dinoflorenzi/THOMSON-MO-TO-SOUNDCARD/SN76489AN/IMG_20201018_101340.jpg

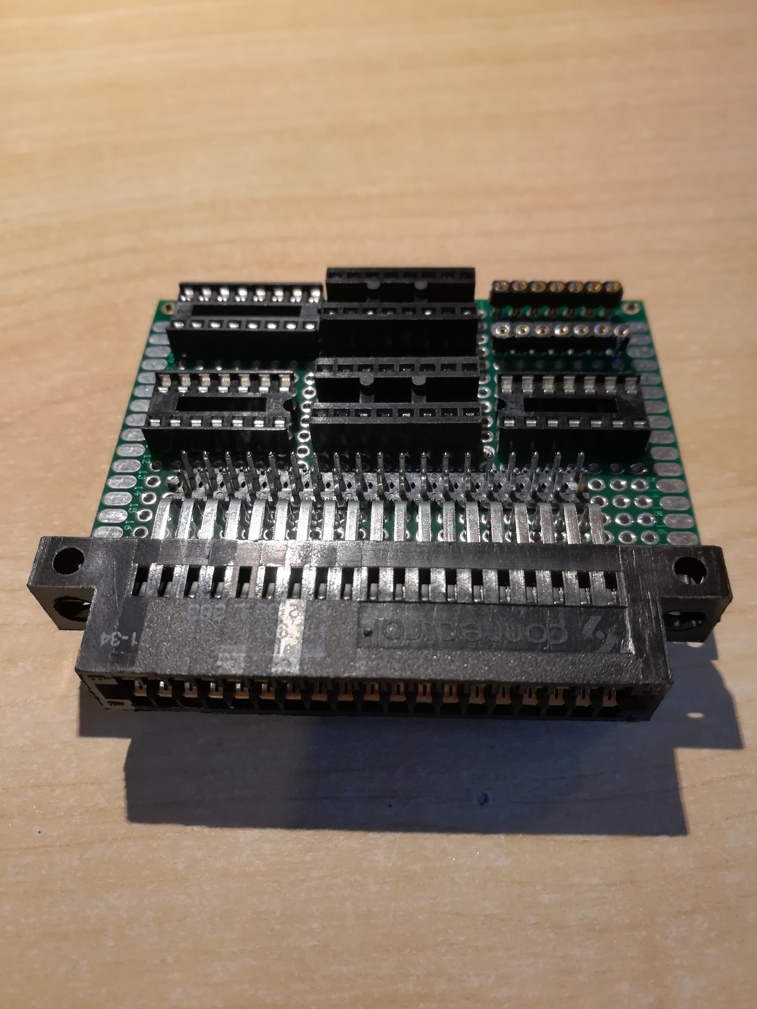
SN76489AN/IMG_20201018_101340.jpg
