dinoflorenzi/THOMSON-MO-TO-SOUNDCARD/SN76489AN/IMG_20201108_161605.jpg

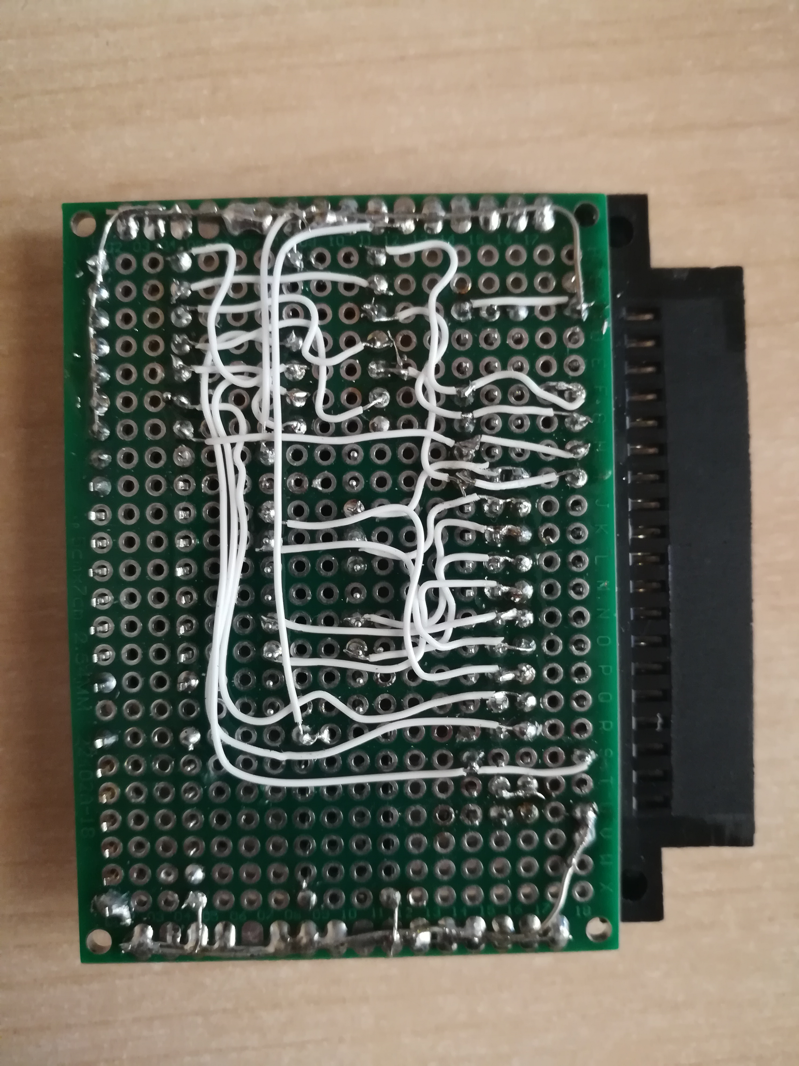
SN76489AN/IMG_20201108_161605.jpg
