dinoflorenzi/THOMSON-MO-TO-SOUNDCARD/SN76489AN/IMG_20201115_202511.jpg

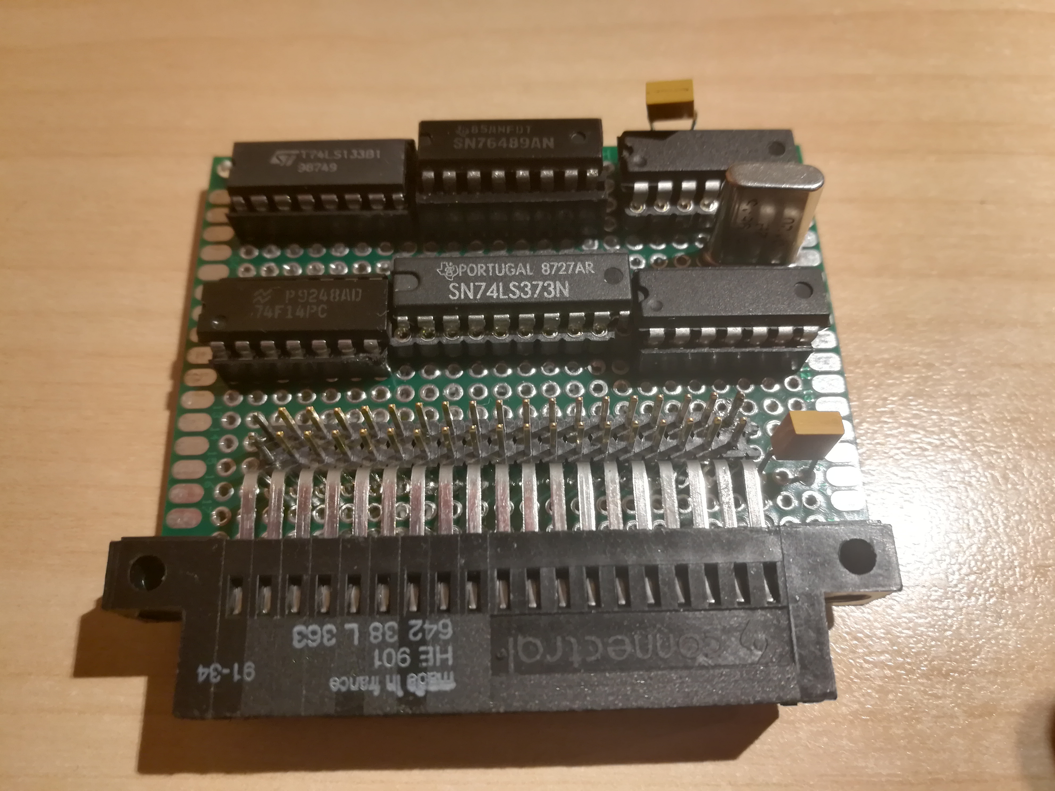
SN76489AN/IMG_20201115_202511.jpg
