dinoflorenzi/THOMSON-MO-TO-SOUNDCARD/SN76489AN/IMG_20210108_192748.jpg

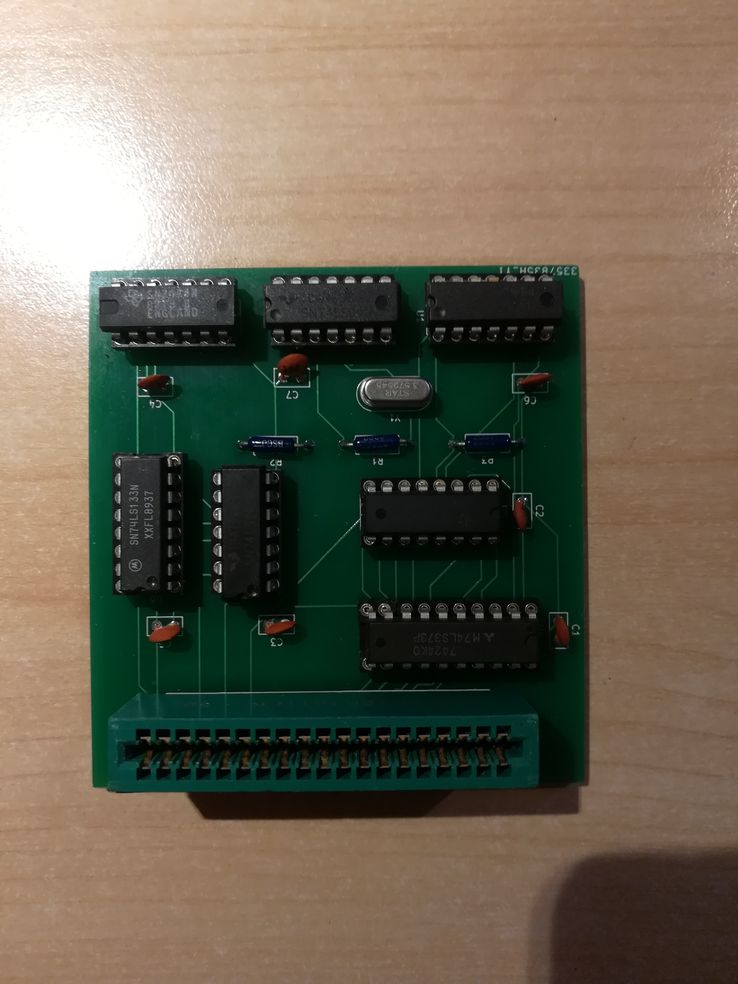
SN76489AN/IMG_20210108_192748.jpg
