dinoflorenzi/THOMSON-MO-TO-SOUNDCARD/SN76489AN/SN76489_MOTO.png

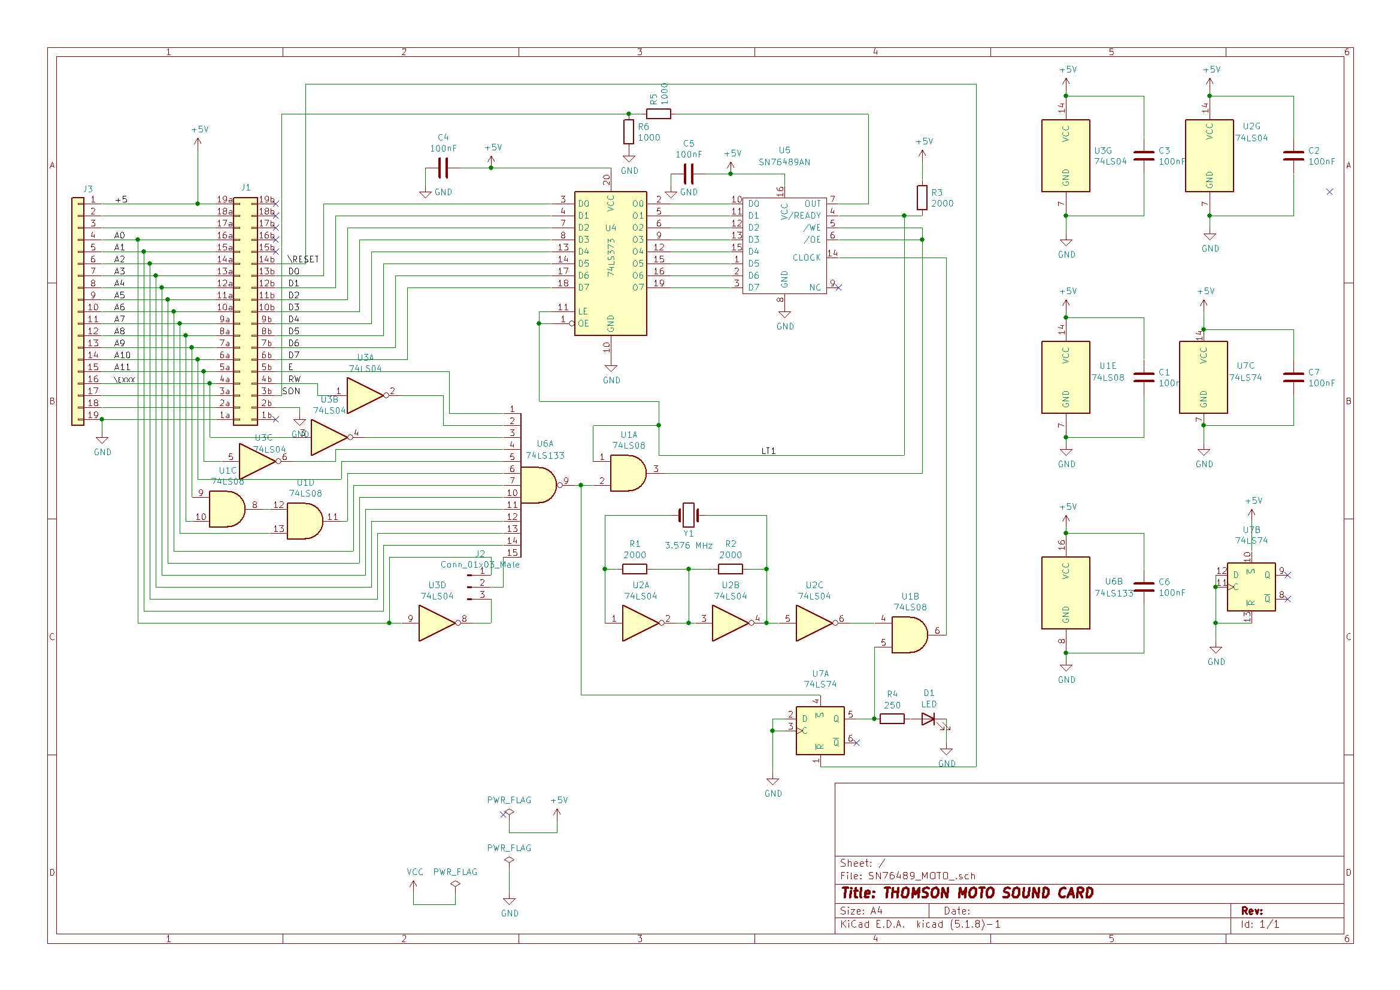
SN76489AN/SN76489_MOTO.png
