dinoflorenzi/THOMSON-MO-TO-SOUNDCARD/SN76489AN/sn76489_REV2.jpg

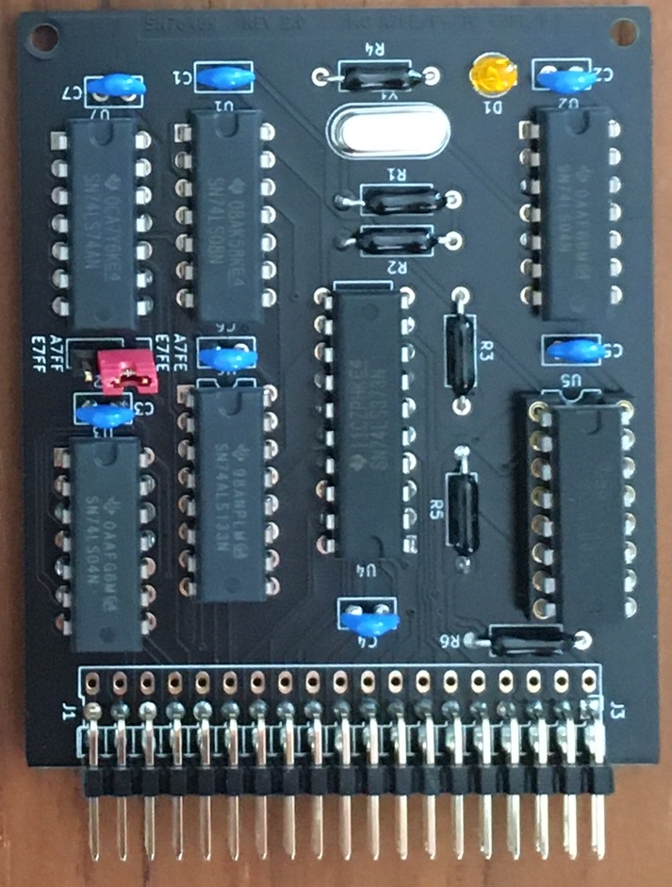
SN76489AN/sn76489_REV2.jpg
