dinoflorenzi/THOMSON-MO-TO-SOUNDCARD/YM2413/IMG_20210620_180053.jpg

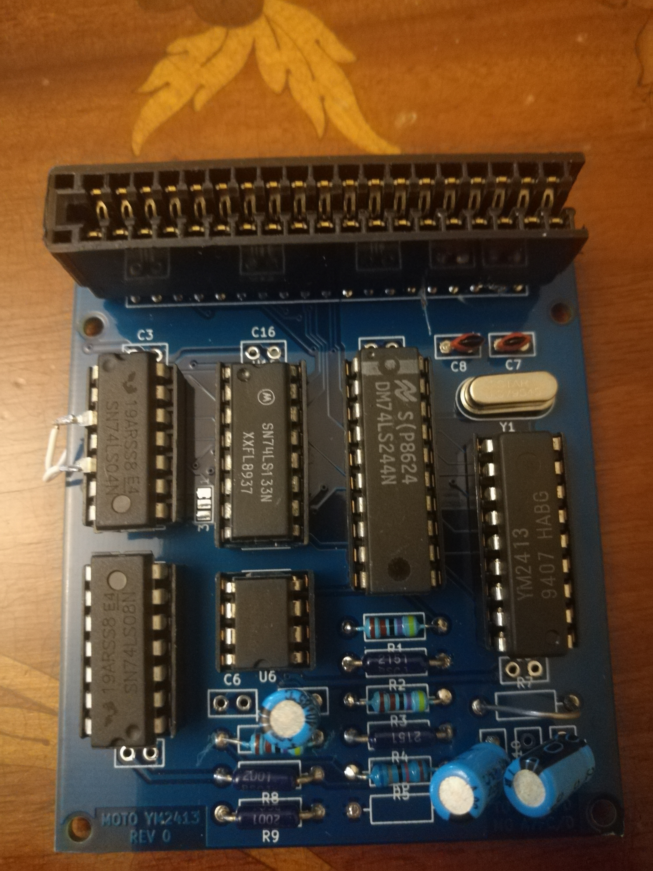
YM2413/IMG_20210620_180053.jpg
