dinoflorenzi/THOMSON-MO-TO-SOUNDCARD/YM2413/REV2/YM2413_FOOL_054410.png

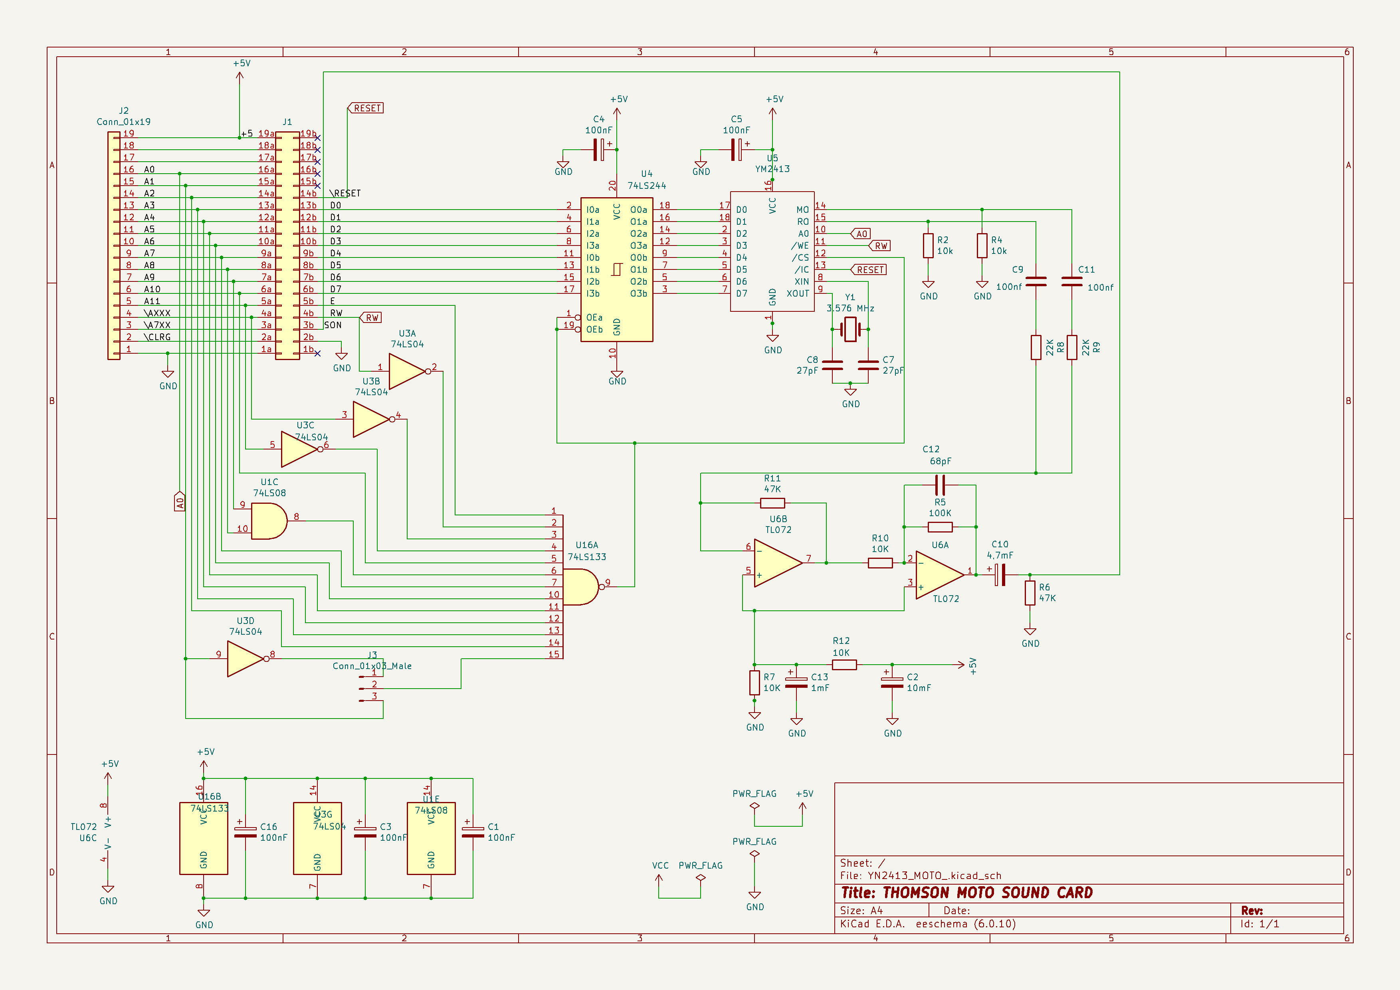
YM2413/REV2/YM2413_FOOL_054410.png
