dinoflorenzi/THOMSON-MO-TO-SOUNDCARD/YM2413/YM2413_MOTO.jpg

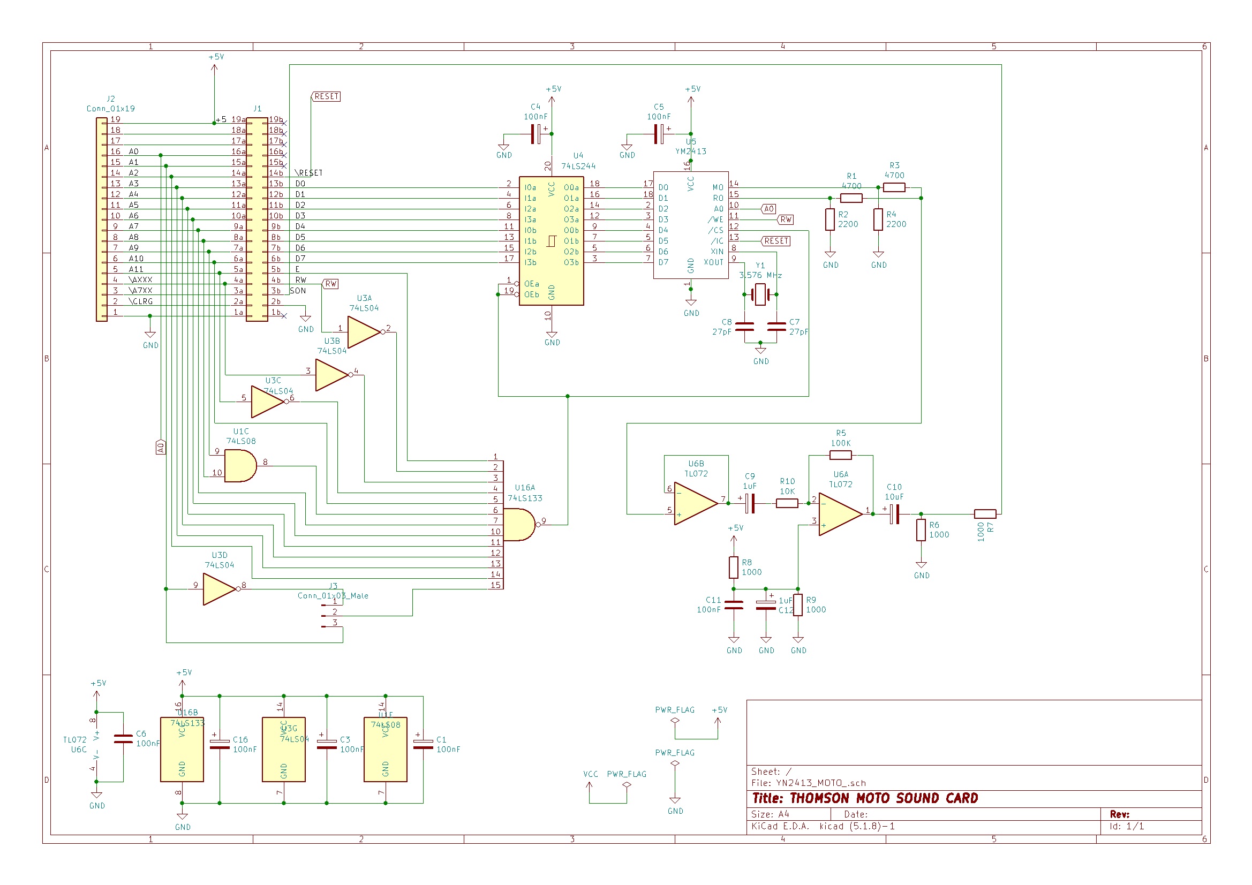
YM2413/YM2413_MOTO.jpg
