dinoflorenzi/THOMSON-MO-TO-SOUNDCARD/YM2413/YM2413_REV1.jpg

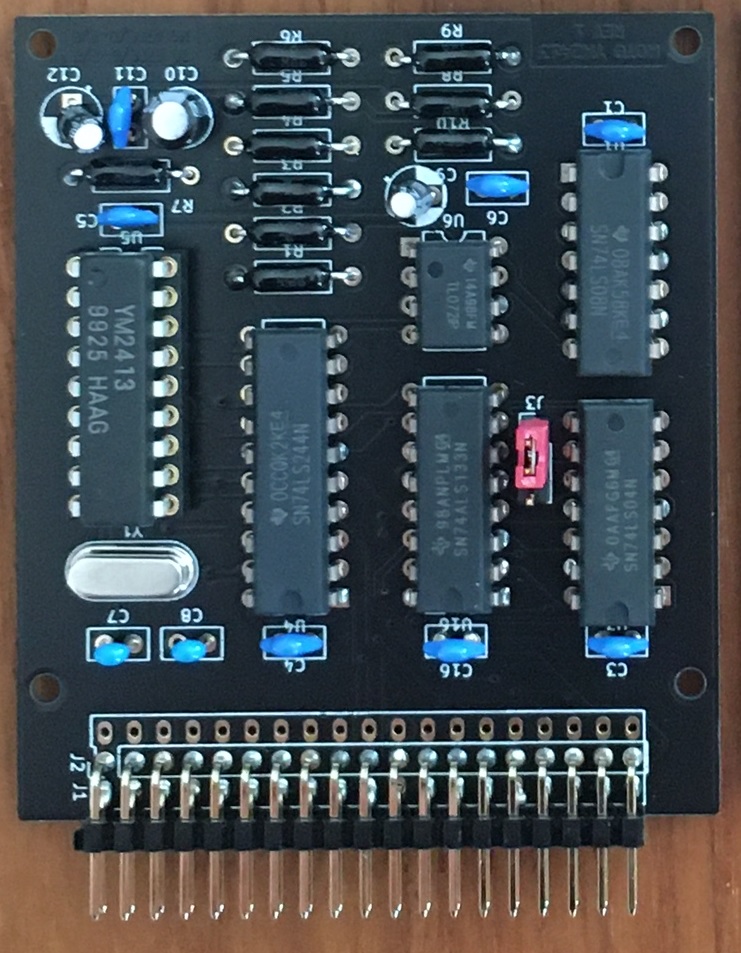
YM2413/YM2413_REV1.jpg
